Autofabricantes/H4_Henar-4/01_Documentation/00_SystemDiagrams/H4_Diagram_FullSystem.png

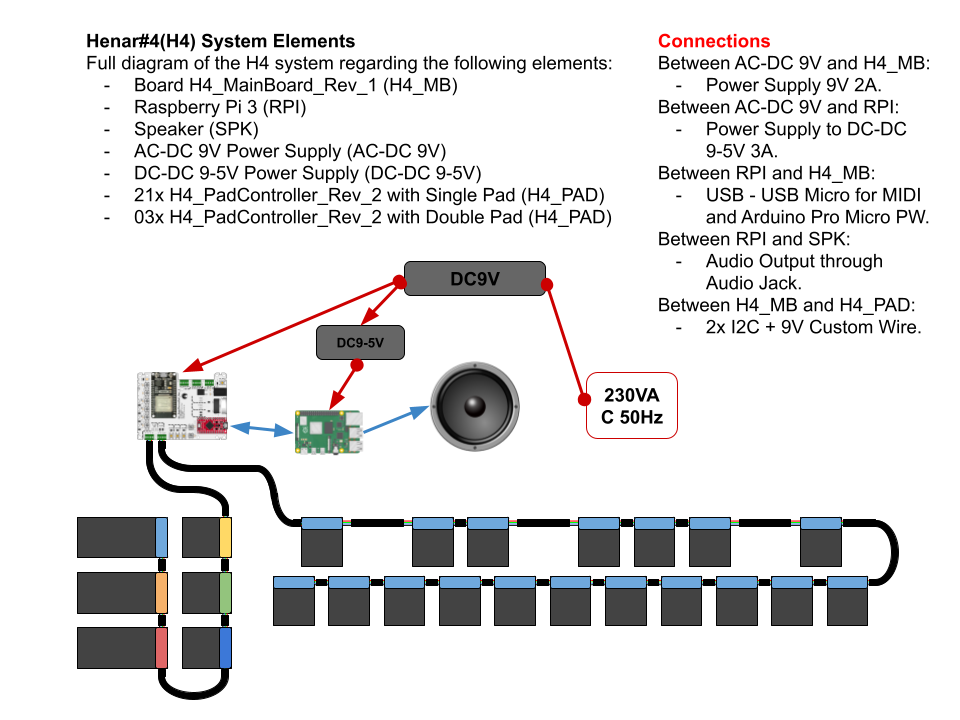
01_Documentation/00_SystemDiagrams/H4_Diagram_FullSystem.png
