Autofabricantes/H4_Henar-4/01_Documentation/00_SystemDiagrams/H4_Diagram_Instrument.png

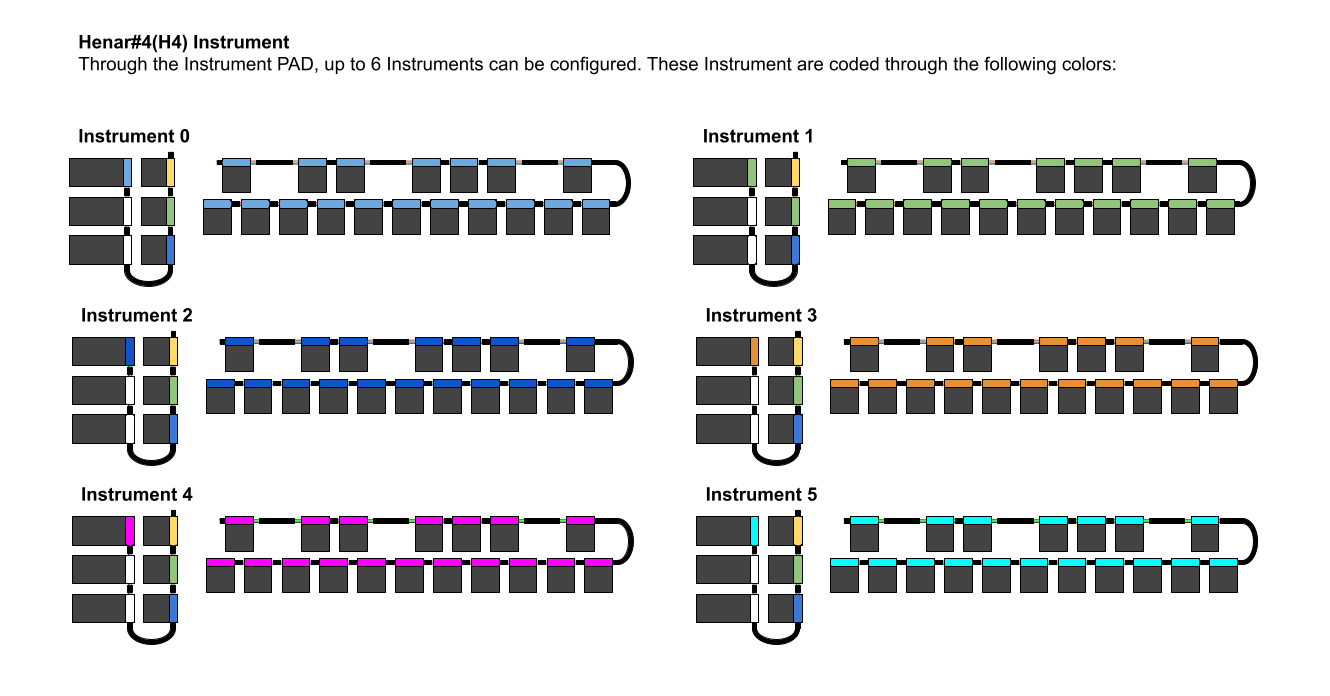
01_Documentation/00_SystemDiagrams/H4_Diagram_Instrument.png
