Autofabricantes/H4_Henar-4/01_Documentation/00_SystemDiagrams/H4_PanelDesign_00.png

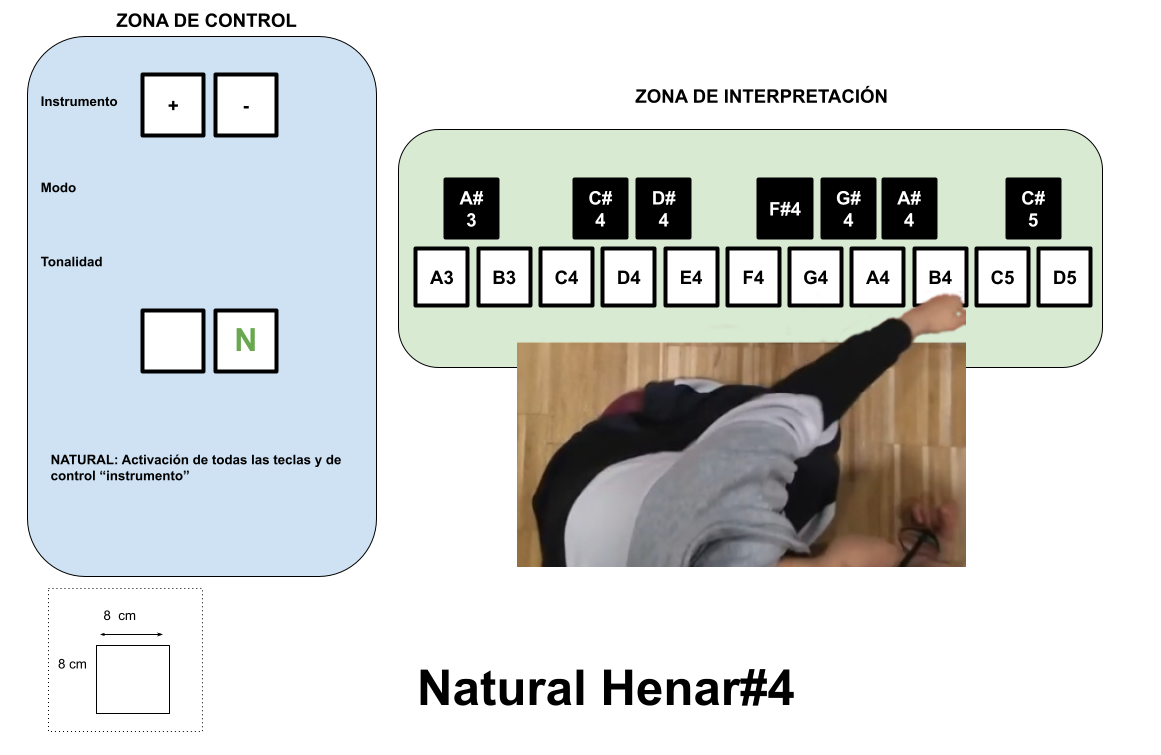
01_Documentation/00_SystemDiagrams/H4_PanelDesign_00.png
