Autofabricantes/H4_Henar-4/01_Documentation/01_OtherImages/H4_RandomPic_00.JPG

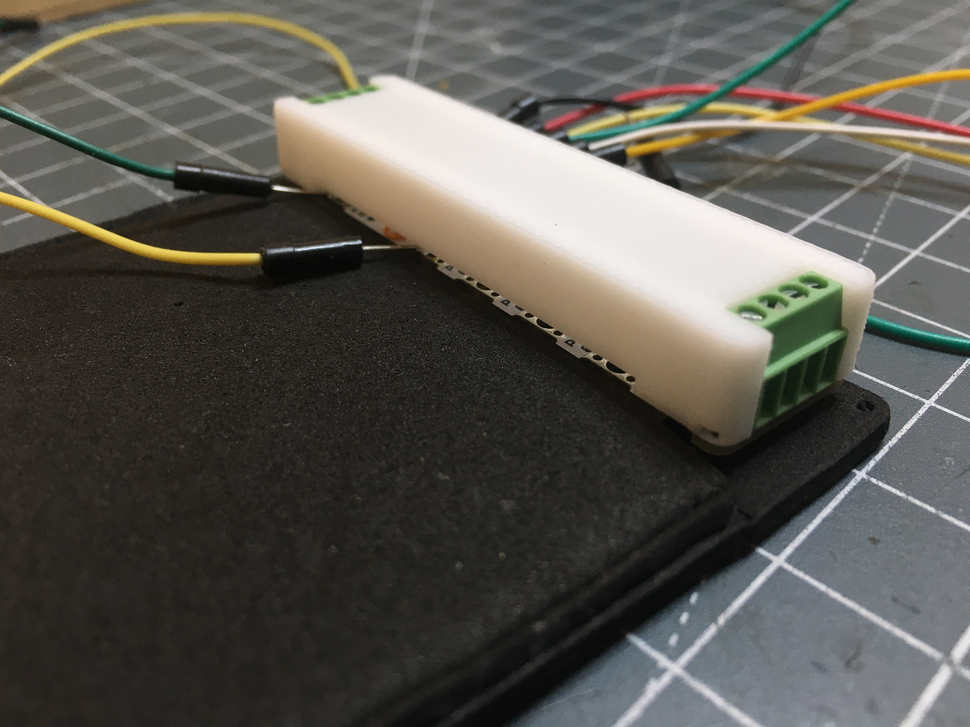
01_Documentation/01_OtherImages/H4_RandomPic_00.JPG
