Autofabricantes/H4_Henar-4/01_Documentation/photo5803215736133498770.jpg

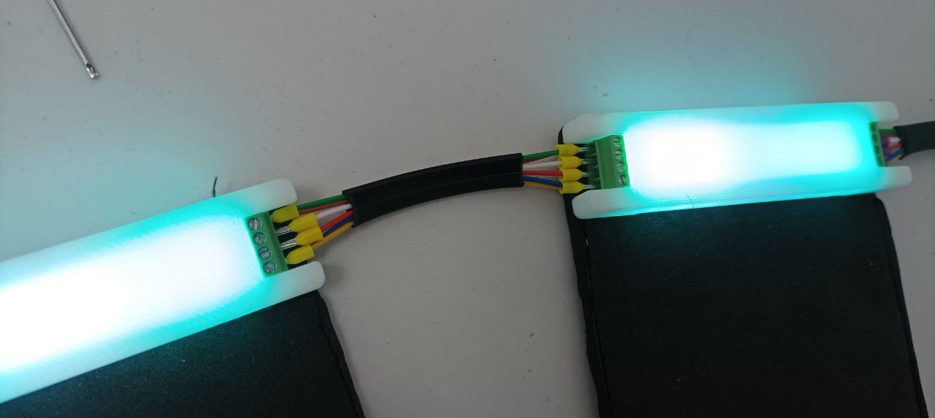
01_Documentation/photo5803215736133498770.jpg
