Autofabricantes/H4_Henar-4/02_Elements/H4_MainController_Rev_1/02_HW/eagleUp/eagleUp_H4_MainController_Rev_1_board_bottom.png

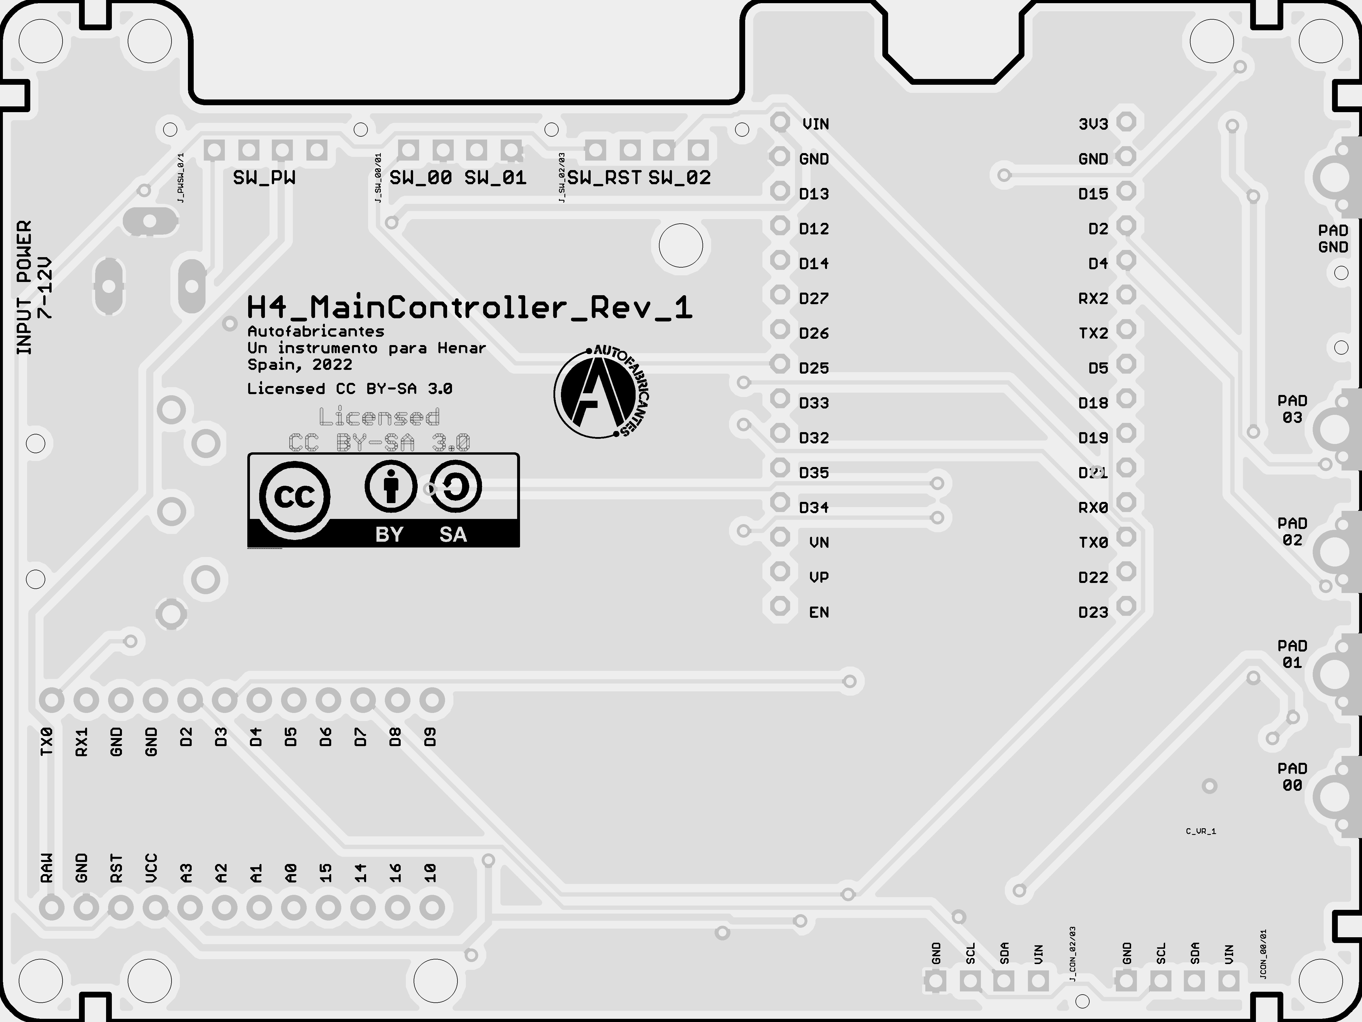
02_Elements/H4_MainController_Rev_1/02_HW/eagleUp/eagleUp_H4_MainController_Rev_1_board_bottom.png
