Autofabricantes/H4_Henar-4/02_Elements/H4_PadController_Rev_2/00_Documentation/H4_Pad_02.png

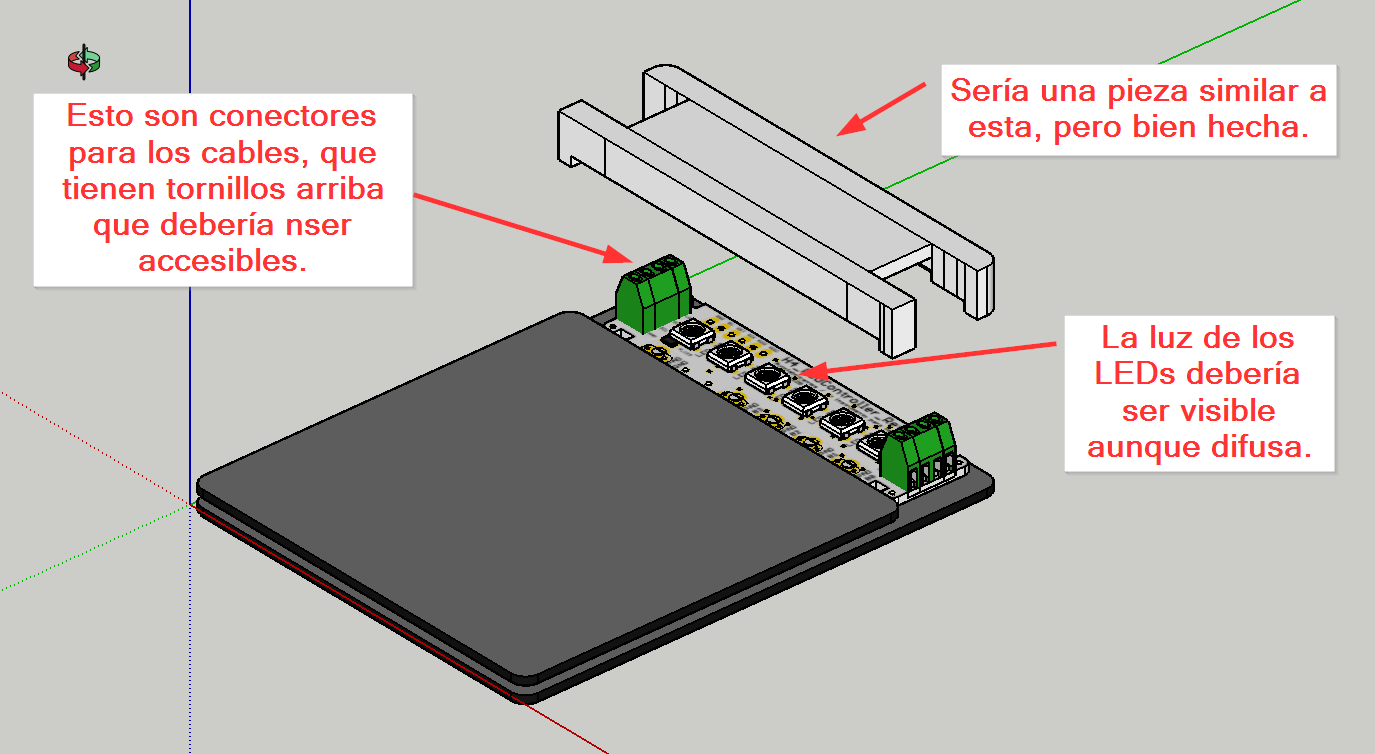
02_Elements/H4_PadController_Rev_2/00_Documentation/H4_Pad_02.png
