Autofabricantes/H4_Henar-4/02_Elements/H4_PadController_Rev_2/00_Documentation/H4_PadController_Rev_1_3DModel/eagleUp_H4_PadController_Rev_1_top_board2.png

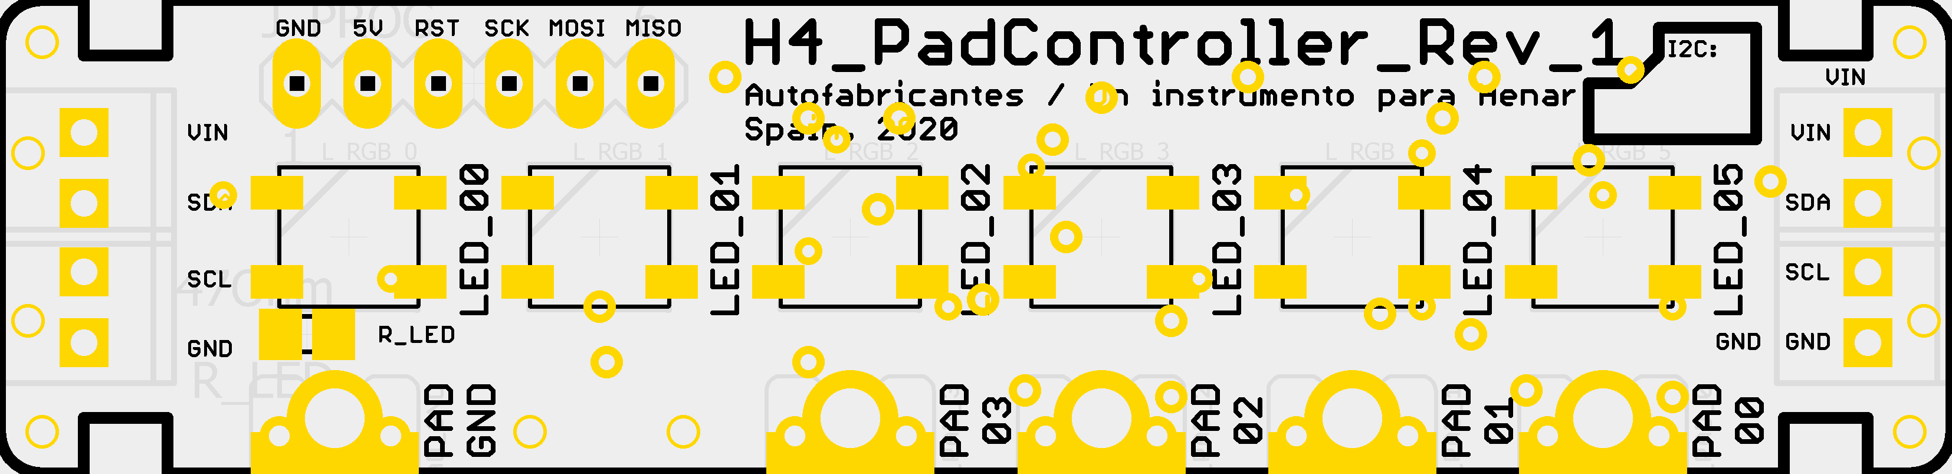
02_Elements/H4_PadController_Rev_2/00_Documentation/H4_PadController_Rev_1_3DModel/eagleUp_H4_PadController_Rev_1_top_board2.png
