Autofabricantes/H4_Henar-4/02_Elements/H4_PadController_Rev_2/00_Documentation/H4_PadController_Rev_1_3DModel/H4_PadController_Rev_1_3DModel_TOP.png

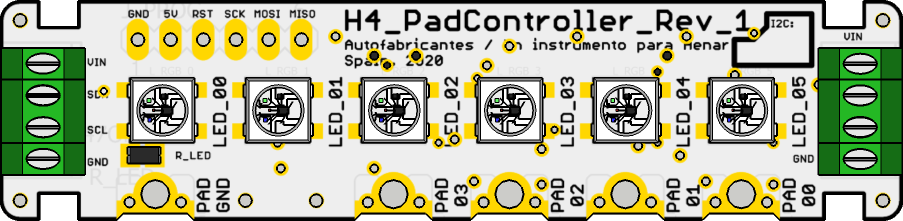
02_Elements/H4_PadController_Rev_2/00_Documentation/H4_PadController_Rev_1_3DModel/H4_PadController_Rev_1_3DModel_TOP.png
