Autofabricantes/H4_Henar-4/02_Elements/H4_PadController_Rev_2/00_Documentation/H4_Velostat_00.png

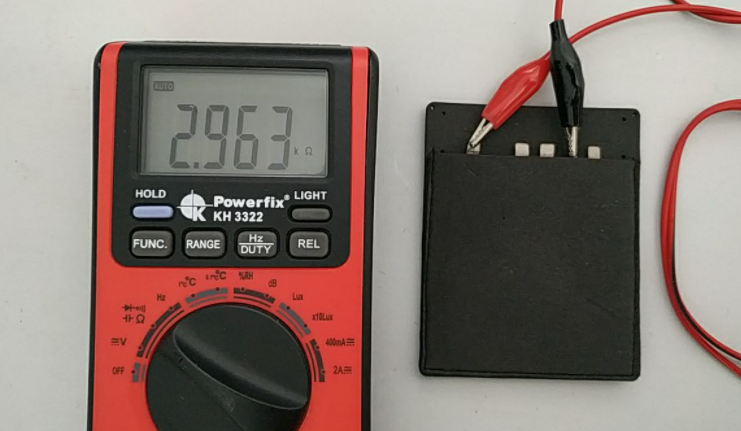
02_Elements/H4_PadController_Rev_2/00_Documentation/H4_Velostat_00.png
