Autofabricantes/H4_Henar-4/01_Documentation/01_OtherImages/H4_ProgrammingGuide_02.png

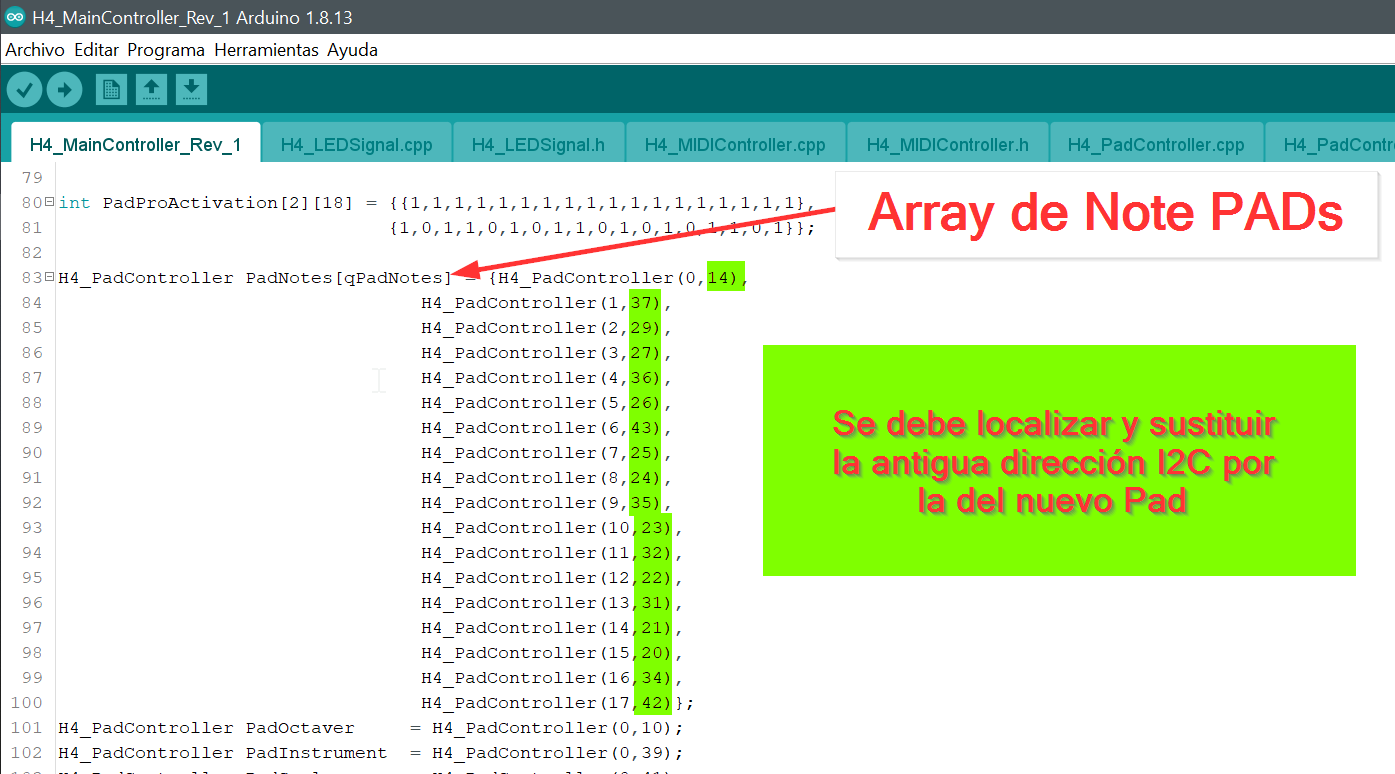
01_Documentation/01_OtherImages/H4_ProgrammingGuide_02.png
