Autofabricantes/H4_Henar-4/02_Elements/H4_MainController_Rev_1/00_Documentation/H4_MainController_Fix_00.png

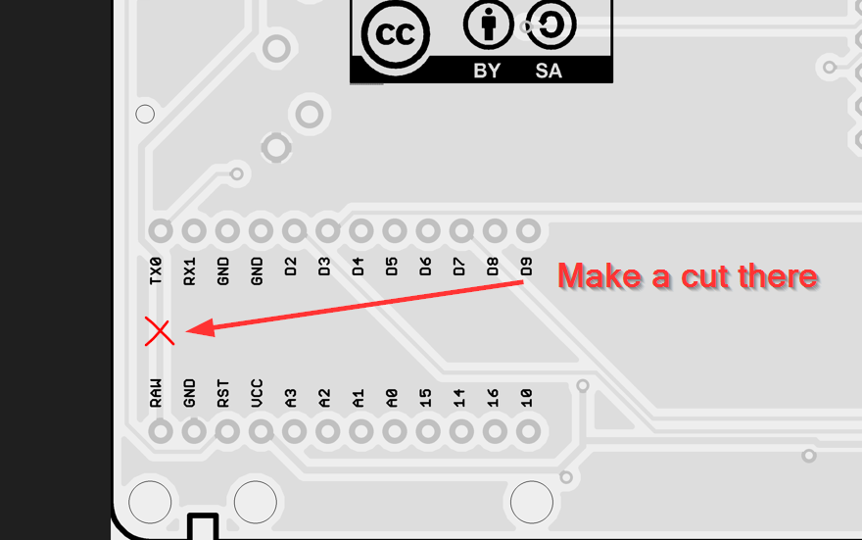
02_Elements/H4_MainController_Rev_1/00_Documentation/H4_MainController_Fix_00.png
