Autofabricantes/H4_Henar-4/02_Elements/H4_MainController_Rev_1/02_HW/H4_MainController_Rev_1.sch

## EAGLE design 02_Elements/H4_MainController_Rev_1/02_HW/H4_MainController_Rev_1.sch (2022-05-10)

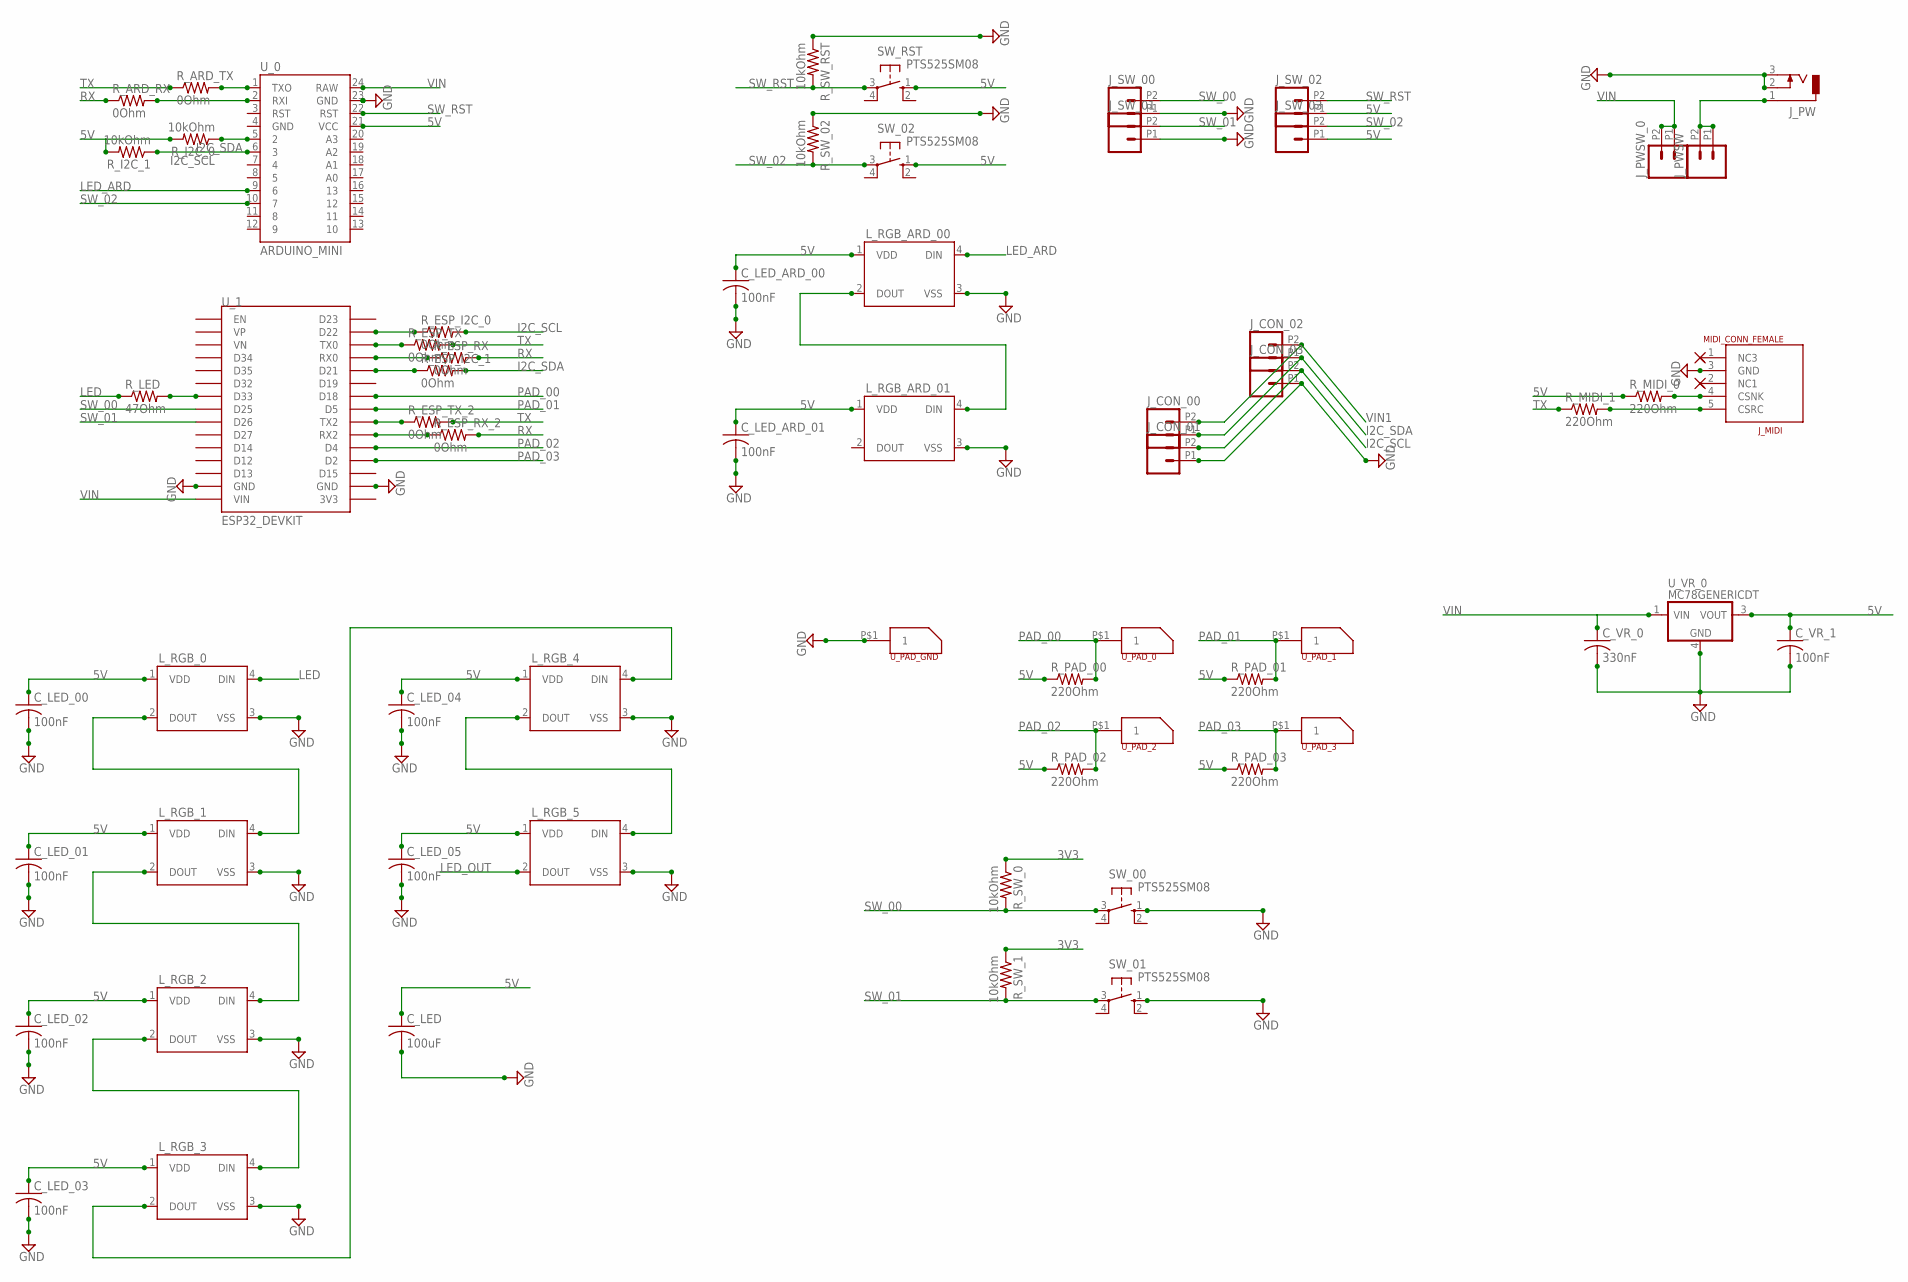
[picture p64: schematic H4_MainController_Rev_1.sch]

Parts:
C_LED: 100uF; C1210
C_LED_00, C_LED_01, C_LED_02, C_LED_03, C_LED_04, C_LED_05: 100nF; C0805K
C_LED_ARD_00, C_LED_ARD_01: 100nF; C0805K
C_VR_0: 330nF; C0805
C_VR_1: 100nF; C0805
J_CON_00, J_CON_01, J_CON_02, J_CON_03: M022.54MM_SCREWTERM; 1X02_2.54_SCREWTERM
J_MIDI: MIDI_CONN_FEMALE; DIN_5_FEMALE
J_PW: DCJ0303
J_PWSW: M022.54MM_SCREWTERM; 1X02_2.54_SCREWTERM
J_PWSW_0: M022.54MM_SCREWTERM; 1X02_2.54_SCREWTERM
J_SW_00, J_SW_01, J_SW_02, J_SW_03: M022.54MM_SCREWTERM; 1X02_2.54_SCREWTERM
L_RGB_0, L_RGB_1, L_RGB_2, L_RGB_3, L_RGB_4, L_RGB_5: WS2812B
L_RGB_ARD_00, L_RGB_ARD_01: WS2812B
R_ARD_RX: 0Ohm; M0805
R_ARD_TX: 0Ohm; M0805
R_ESP_I2C_0, R_ESP_I2C_1: 0Ohm; M0805
R_ESP_RX: 0Ohm; M0805
R_ESP_RX_2: 0Ohm; M0805
R_ESP_TX: 0Ohm; M0805
R_ESP_TX_2: 0Ohm; M0805
R_I2C_0, R_I2C_1: 10kOhm; M0805
R_LED: 47Ohm; M0805
R_MIDI_0, R_MIDI_1: 220Ohm; M0805
R_PAD_00, R_PAD_01, R_PAD_02, R_PAD_03: 220Ohm; M0805
R_SW_0, R_SW_1, R_SW_02: 10kOhm; M0805
R_SW_RST: 10kOhm; M0805
SW_00, SW_01, SW_02: PTS525SM08; SM08
SW_RST: PTS525SM08; SM08
U_0: ARDUINO_MINI
U_1: ESP32_DEVKIT
U_PAD_0, U_PAD_1, U_PAD_2, U_PAD_3: PAD_CONNECTOR_MULTI
U_PAD_GND: PAD_CONNECTOR_MULTI
U_VR_0: MC78GENERICDT; DPAK-3

Connections:
3V3: R_SW_0.1, R_SW_1.1
5V: C_LED.1, C_LED_00.1, C_LED_01.1, C_LED_02.1, C_LED_03.1, C_LED_04.1, C_LED_05.1, C_LED_ARD_00.1, C_LED_ARD_01.1, C_VR_1.1, J_SW_02.P1 (1), J_SW_03.P1 (1), L_RGB_0.1 (VDD), L_RGB_1.1 (VDD), L_RGB_2.1 (VDD), L_RGB_3.1 (VDD), L_RGB_4.1 (VDD), L_RGB_5.1 (VDD), L_RGB_ARD_00.1 (VDD), L_RGB_ARD_01.1 (VDD), R_I2C_0.2, R_I2C_1.2, R_MIDI_0.1, R_PAD_00.1, R_PAD_01.1, R_PAD_02.1, R_PAD_03.1, SW_02.1 (S), SW_RST.1 (S), U_0.21 (VCC), U_VR_0.3 (VOUT)
GND: C_LED.2, C_LED_00.2, C_LED_01.2, C_LED_02.2, C_LED_03.2, C_LED_04.2, C_LED_05.2, C_LED_ARD_00.2, C_LED_ARD_01.2, C_VR_0.2, C_VR_1.2, J_CON_01.P1 (1), J_CON_03.P1 (1), J_MIDI.3 (GND), J_PW.2, J_PW.3, J_SW_00.P1 (1), J_SW_01.P1 (1), L_RGB_0.3 (VSS), L_RGB_1.3 (VSS), L_RGB_2.3 (VSS), L_RGB_3.3 (VSS), L_RGB_4.3 (VSS), L_RGB_5.3 (VSS), L_RGB_ARD_00.3 (VSS), L_RGB_ARD_01.3 (VSS), R_SW_02.1, R_SW_RST.1, SW_00.1 (S), SW_01.1 (S), U_0.23 (GND), U_1.GND@1 (GND), U_1.GND@2 (GND), U_PAD_GND.P$1, U_VR_0.4 (GND)
I2C_SCL: J_CON_01.P2 (2), J_CON_03.P2 (2), R_ESP_I2C_0.2, R_I2C_1.1, U_0.6 (3)
I2C_SDA: J_CON_00.P1 (1), J_CON_02.P1 (1), R_ESP_I2C_1.2, R_I2C_0.1, U_0.5 (2)
LED: L_RGB_0.4 (DIN), R_LED.1
LEDE: L_RGB_3.2 (DOUT), L_RGB_4.4 (DIN)
LED_ARD: L_RGB_ARD_00.4 (DIN), U_0.9 (6)
LED_OUT: L_RGB_5.2 (DOUT)
unnamed: R_ESP_TX.1, U_1.TX0
unnamed: R_ESP_RX.1, U_1.RX0
unnamed: L_RGB_2.2 (DOUT), L_RGB_3.4 (DIN)
unnamed: J_MIDI.4 (CSNK), R_MIDI_0.2
unnamed: R_ARD_TX.2, U_0.1 (TXO)
unnamed: R_ARD_RX.2, U_0.2 (RXI)
unnamed: R_ESP_TX_2.1, U_1.TX2
unnamed: R_LED.2, U_1.D33
unnamed: L_RGB_1.2 (DOUT), L_RGB_2.4 (DIN)
unnamed: L_RGB_0.2 (DOUT), L_RGB_1.4 (DIN)
unnamed: R_ESP_RX_2.1, U_1.RX2
unnamed: L_RGB_ARD_00.2 (DOUT), L_RGB_ARD_01.4 (DIN)
unnamed: J_MIDI.5 (CSRC), R_MIDI_1.2
unnamed: L_RGB_4.2 (DOUT), L_RGB_5.4 (DIN)
unnamed: R_ESP_I2C_0.1, U_1.D22
unnamed: R_ESP_I2C_1.1, U_1.D21
unnamed: J_PW.1, J_PWSW.P1 (1), J_PWSW.P2 (2)
PAD_00: R_PAD_00.2, U_1.D18, U_PAD_0.P$1
PAD_01: R_PAD_01.2, U_1.D5, U_PAD_1.P$1
PAD_02: R_PAD_02.2, U_1.D4, U_PAD_2.P$1
PAD_03: R_PAD_03.2, U_1.D2, U_PAD_3.P$1
RX: R_ARD_RX.1, R_ESP_RX.2, R_ESP_RX_2.2
SW_00: J_SW_00.P2 (2), R_SW_0.2, SW_00.3, U_1.D25
SW_01: J_SW_01.P2 (2), R_SW_1.2, SW_01.3, U_1.D26
SW_02: J_SW_03.P2 (2), R_SW_02.2, SW_02.3, U_0.10 (7)
SW_RST: J_SW_02.P2 (2), R_SW_RST.2, SW_RST.3, U_0.22 (RST)
TX: R_ARD_TX.1, R_ESP_TX.2, R_ESP_TX_2.2, R_MIDI_1.1
VIN: C_VR_0.1, J_PWSW_0.P1 (1), J_PWSW_0.P2 (2), U_0.24 (RAW), U_1.VIN, U_VR_0.1 (VIN)
VIN1: J_CON_00.P2 (2), J_CON_02.P2 (2)
