Autofabricantes/H4_Henar-4/02_Elements/H4_MainController_Rev_1/03_SW/H4_MainController_Rev_1/H4_MIDIController.cpp

/*
 * @author Pablo dMM (Pablodmm.isp@gmail.com)
 * @brief  Part of the Henar#4 Project. https://github.com/Autofabricantes/Henar-4 .
 * @date   2022_02_13
 */
 // Library Import
#include "Arduino.h"
#include "H4_MIDIController.h"
#include <MIDIUSB.h>
/**
 * @brief H4_MIDIController Constructor.
 */
H4_MIDIController::H4_MIDIController()
{

}

/**
 * @brief Sends a MIDI Message through Serial
 * @param MIDICHANNEL
 * @param MESSAGE
 * @param PITCH
 * @param VELOCITY
 */	
void H4_MIDIController::MIDI_TX(byte MIDICHANNEL, byte MESSAGE, byte PITCH, byte VELOCITY) {
  //byte status1 = MESSAGE + MIDICHANNEL;
  //Serial.write(MESSAGE + MIDICHANNEL);
  //Serial.write(PITCH);
  //Serial.write(VELOCITY);
  midiEventPacket_t event = {(byte)(MESSAGE >> 4), (byte)(MESSAGE | (MIDICHANNEL)), PITCH, VELOCITY};
  MidiUSB.sendMIDI(event);
  MidiUSB.flush();
}

/**
 * @brief Sends a OFF Note signal from INIT_NOTE to END_NOTE
 * @param CHANNEL	The Channel in which to send the Note message
 * @param INIT_NOTE
 * @param END_NOTE
 */
void H4_MIDIController::MIDIOFF_FIX(byte CHANNEL, int INIT_NOTE, int END_NOTE){ // This is a very rude and nasty sustitution to a General Note Off CMD
  for(int i= INIT_NOTE; i <= END_NOTE; i++){
    MIDI_TX(CHANNEL, NOTE_OFF, i, 0);
    delay(10);
  }
}
